delan/usb3sun/doc/attic/mapping.txt

1	0x05	0x85	F1	58
2	0x06	0x86	F2	59
3	0x08	0x88	F3	60
4	0x0A	0x8A	F4	61
5	0x0C	0x8C	F5	62
6	0x0E	0x8E	F6	63
7	0x10	0x90	F7	64
8	0x11	0x91	F8	65
9	0x12	0x92	F9	66
10	0x07	0x87	F10	67
11	0x09	0x89	F11	68
12	0x0B	0x8B	F12	69
13	0x58	0xD8	\	|	100
14	0x42	0xC2	Delete	76
15	0x01	0x81	Stop	120**
16	0x03	0x83	Again	121**
17	0x15	0x95	Pause	72***
18	0x16	0x96	Pr Sc	70***
19	0x17	0x97	Break	Scroll Lock	71(72?)***
20	0x62	0xE2	Num Lock	83
21	0x19	0x99	Props	163**
22	0x1A	0x9A	Undo	122**
23	0x1D	0x9D	Esc	41
24	0x1E	0x9E	1	!	30
25	0x1F	0x9F	2	@	31
26	0x20	0xA0	3	#	32
27	0x21	0xA1	4	$	33
28	0x22	0xA2	5	%	34
29	0x23	0xA3	6	^	35
30	0x24	0xA4	7	&	36
31	0x25	0xA5	8	*	37
32	0x26	0xA6	9	(	38
33	0x27	0xA7	0	)	39
34	0x28	0xA8	-	_	45
35	0x29	0xA9	=	+	46
36	0x2B	0xAB	Backspace	42
37	0x2D	0xAD	=	103**
38	0x2E	0xAE	/	84
39	0x2F	0xAF	*	85
40	0x47	0xC7	-	86
41	0x31	0xB1	Front	?
42	0x33	0xB3	Copy	124**
43	0x35	0xB5	Tab	43
44	0x36	0xB6	Q	20
45	0x37	0xB7	W	26
46	0x38	0xB8	E	8
47	0x39	0xB9	R	21
48	0x3A	0xBA	T	23
49	0x3B	0xBB	Y	28
50	0x3C	0xBC	U	24
51	0x3D	0xBD	I	12
52	0x3E	0xBE	O	18
53	0x3F	0xEF	P	19
54	0x40	0xC0	[	{	47
55	0x41	0xC1	]	}	48
56	0x59	0xD9	Return	158(40?)**
57	0x44	0xC4	Home	7	95
58	0x45	0xC5	(up cur)	8	96
59	0x46	0xC6	PgUp	9	97
60	0x7D	0xFD	+	87
61	0x48	0xC8	Open	?
62	0x49	0xC9	Paste	125**
63	0x4C	0xCC	Control	CtrlL*
64	0x4D	0xCD	A	4
65	0x4E	0xCE	S	22
66	0x4F	0xCF	D	7
67	0x50	0xD0	F	9
68	0x51	0xD1	G	10
69	0x52	0xD2	H	11
70	0x53	0xD3	J	13
71	0x54	0xD4	K	14
72	0x55	0xD5	L	15
73	0x56	0xD6	;	:	51
74	0x57	0xD7	'	"	52
75	0x2A	0xAA	`	~	53
76	0x5B	0xDB	(Left Cur)	4	92
77	0x5C	0xDC	5	93
78	0x5D	0xDD	(Right Cur)	6	94
79	0x5F	0xDF	Find	126**
80	0x61	0xE1	Cut	123**
81	0x63	0xE3	Shift	ShiftL*
82	0x64	0xE4	Z	29
83	0x65	0xE5	X	27
84	0x66	0xE6	C	6
85	0x67	0xE7	V	25
86	0x68	0xE8	B	5
87	0x69	0xE9	N	17
88	0x6A	0xEA	M	16
89	0x6B	0xEB	,	<	54
90	0x6C	0xEC	.	>	55
91	0x6D	0xED	/	?	56
92	0x6E	0xEE	Shift	ShiftR*
93	0x6F	0xEF	Line Feed	?
94	0x70	0xF0	End	1	89
95	0x71	0xF1	(Dn Cur)	2	90
96	0x72	0xF2	PgDn	3	91
97	0x5A	0xDA	Enter	88
98	0x76	0xF6	Help	117**
99	0x77	0xF7	Caps Lock	57
100	0x13	0x93	Alt	AltL*
101	0x78	0xF8	(L Triangle)	GuiL*
102	0x79	0xF9	(Space Bar)	44
103	0x7A	0xFA	(R triangle)	GuiR*
104	0x43	0xC3	Compose	?
105	0x0D	0x8D	Graph	Alt	AltR*
106	0x5E	0xDE	Ins	0	98
107	0x32	0xB2	Del	.	99
