delan/usb3sun/tusb_config.h

// usb3sun note!
// platformio incremental build is unaware of this file.
// if you change it, do a clean build or touch the build_flags.

/*
 * The MIT License (MIT)
 *
 * Copyright (c) 2019 Ha Thach (tinyusb.org)
 *
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
 */

#ifndef _TUSB_CONFIG_H_
#define _TUSB_CONFIG_H_

#ifdef __cplusplus
 extern "C" {
#endif

//--------------------------------------------------------------------
// COMMON CONFIGURATION
//--------------------------------------------------------------------

#ifndef CFG_TUSB_MCU
 #define CFG_TUSB_MCU             OPT_MCU_RP2040
#endif

#define CFG_TUSB_RHPORT0_MODE     OPT_MODE_DEVICE
#define CFG_TUSB_OS               OPT_OS_PICO

// CFG_TUSB_DEBUG is defined by compiler in DEBUG build
#ifndef CFG_TUSB_DEBUG
#define CFG_TUSB_DEBUG           0
#endif

/* USB DMA on some MCUs can only access a specific SRAM region with restriction on alignment.
 * Tinyusb use follows macros to declare transferring memory so that they can be put
 * into those specific section.
 * e.g
 * - CFG_TUSB_MEM SECTION : __attribute__ (( section(".usb_ram") ))
 * - CFG_TUSB_MEM_ALIGN   : __attribute__ ((aligned(4)))
 */
#ifndef CFG_TUSB_MEM_SECTION
#define CFG_TUSB_MEM_SECTION
#endif

#ifndef CFG_TUSB_MEM_ALIGN
#define CFG_TUSB_MEM_ALIGN          __attribute__ ((aligned(4)))
#endif

//--------------------------------------------------------------------
// DEVICE CONFIGURATION
//--------------------------------------------------------------------

#ifndef CFG_TUD_ENDPOINT0_SIZE
#define CFG_TUD_ENDPOINT0_SIZE    64
#endif

//------------- CLASS -------------//
#define CFG_TUD_HID              (2)
#define CFG_TUD_CDC              (1)
#define CFG_TUD_MSC              (0)
#define CFG_TUD_MIDI             (0)
#define CFG_TUD_VENDOR           (0)

#define CFG_TUD_CDC_RX_BUFSIZE  (256)
#define CFG_TUD_CDC_TX_BUFSIZE  (256)

#define CFG_TUD_MIDI_RX_BUFSIZE (64)
#define CFG_TUD_MIDI_TX_BUFSIZE (64)

// HID buffer size Should be sufficient to hold ID (if any) + Data
#define CFG_TUD_HID_EP_BUFSIZE  (64)

// ======= LOCAL ADDITIONS BELOW ======= //

// see <.pio/libdeps/pico/Adafruit TinyUSB Library/src/arduino/ports/rp2040/Adafruit_TinyUSB_rp2040.cpp>
#define CFG_TUSB_DEBUG_PRINTF serial1_printf
// extern "C" {
//   extern int serial2_printf(const char *__restrict __format, ...);
// }

#define CFG_TUH_ENABLED 0
#define CFG_TUH_RPI_PIO_USB 0
#define CFG_TUH_ENUMERATION_BUFSIZE 256
#define CFG_TUH_HUB 1
#define CFG_TUH_DEVICE_MAX 4
#define CFG_TUH_HID 4
// #define CFG_TUH_HID_EPIN_BUFSIZE 64
// #define CFG_TUH_HID_EPOUT_BUFSIZE 64

#ifdef __cplusplus
 }
#endif

#endif /* _TUSB_CONFIG_H_ */
