delan/usb3sun/src/sunk.cc

#include "sunk.h"

#include <cstdint>

#include <Arduino.h>

#include "bindings.h"
#include "buzzer.h"
#include "pinout.h"

void sunkSend(bool make, uint8_t code) {
  static int activeCount = 0;
  if (make) {
    activeCount += 1;
    buzzer.click();
  } else {
    activeCount -= 1;
    code |= SUNK_BREAK_BIT;
  }

#ifdef SUNK_ENABLE
#ifdef SUNK_VERBOSE
  Sprintf("sunk: tx %02Xh\n", code);
#endif
  pinout.sunk->write(code);
#endif

  if (activeCount <= 0) {
    activeCount = 0;
#ifdef SUNK_ENABLE
#ifdef SUNK_VERBOSE
  Sprintf("sunk: idle\n");
#endif
  pinout.sunk->write(SUNK_IDLE);
#endif
  }

  switch (code) {
    case SUNK_POWER:
      Sprintf("sunk: power high\n");
      digitalWrite(POWER_KEY, HIGH);
      break;
    case SUNK_POWER | SUNK_BREAK_BIT:
      Sprintf("sunk: power low\n");
      digitalWrite(POWER_KEY, LOW);
      break;
  }
}
