delan/usb3sun/src/panic.h

#ifndef USB3SUN_PANIC_H
#define USB3SUN_PANIC_H

#include "config.h"
#include "pinout.h"

#include <Arduino.h>

template<typename... Args>
void panic2(const char *fmt, Args... args) {
    Sprint("panic: ");
    Sprintf(fmt, args...);
    Sprintln();
    panic(fmt, args...);
}

#endif
