delan/usb3sun/src/settings.cc

#include "config.h"
#include "settings.h"

#include <LittleFS.h>

void Settings::begin() {
  LittleFSConfig cfg;
  cfg.setAutoFormat(true);
  LittleFS.setConfig(cfg);
  if (LittleFS.begin()) {
    Sprintln("settings: mounted");
  }
}

void Settings::readAll() {
  read(settings.clickDuration_field);
  read(settings.forceClick_field);
  read(settings.mouseBaud_field);
  read(settings.hostid_field);
}
